feraudet/dmxnow/hardware/datasheets/README.md

# Fiches constructeur utilisées pour les empreintes

Les PDF ne sont pas versionnés (droits des fabricants) : les télécharger dans ce dossier
pour la relecture (`hardware/REVIEW.md` §1). Consultées le 2026-09-26.

| Fichier local | Composant | Source | Pages utilisées |
|---|---|---|---|
| `omron-g5rl.pdf` | K1 Omron G5RL-1A-E-HR DC5 | https://omronfs.omron.com/en_US/ecb/products/pdf/en-g5rl.pdf | p. 5 (dimensions, perçages, brochage), caractéristiques bobine et contacts |
| `wago-2604-1102.pdf` | J1, J4, J7, J5 WAGO 2604-1102 (J6 : 2604-1102 ; J8 : 2604-1103, même série) | https://wmsc.lcsc.com/wmsc/upload/file/pdf/v2/lcsc/2404031513_WAGO-2604-1102_C3309286.pdf (fiche WAGO du 18.02.2024) | p. 2 (dimensions), p. 3 (caractéristiques) |
| `meanwell-irm-03.pdf` | PS1 Mean Well IRM-03-5 | https://www.meanwell.com/Upload/PDF/IRM-03/IRM-03-SPEC.PDF (révision 2025-08-08) | p. 4 (mécanique, brochage) |
